ldt9/Stock-Market-BopIt/Enclosure Design Files/ProductImages/IMG_0335.jpg

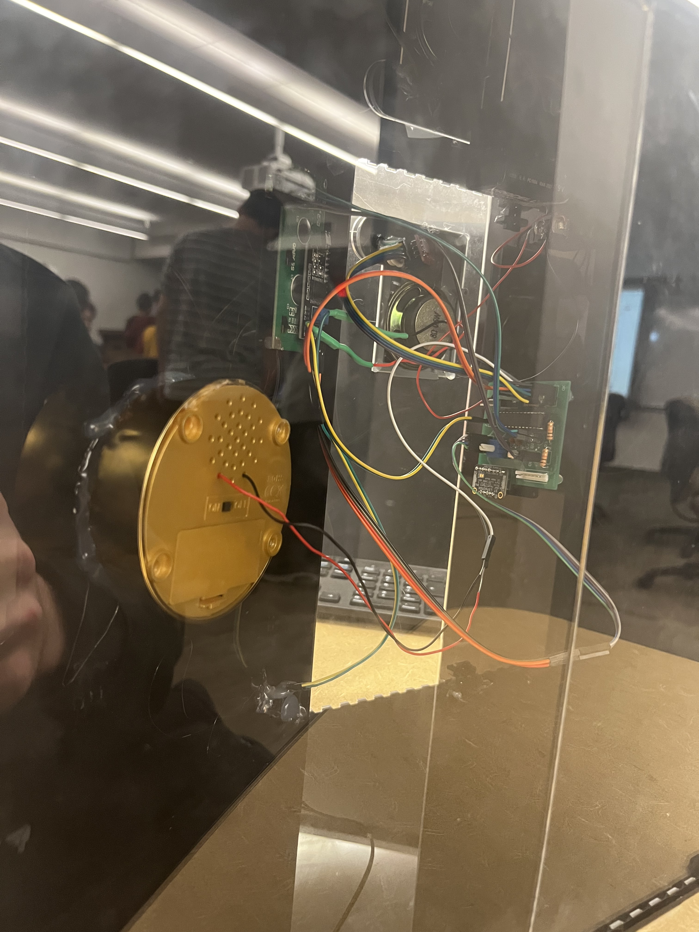
Enclosure Design Files/ProductImages/IMG_0335.jpg
