ldt9/Stock-Market-BopIt/Enclosure Design Files/ProductImages/IMG_0336.jpg

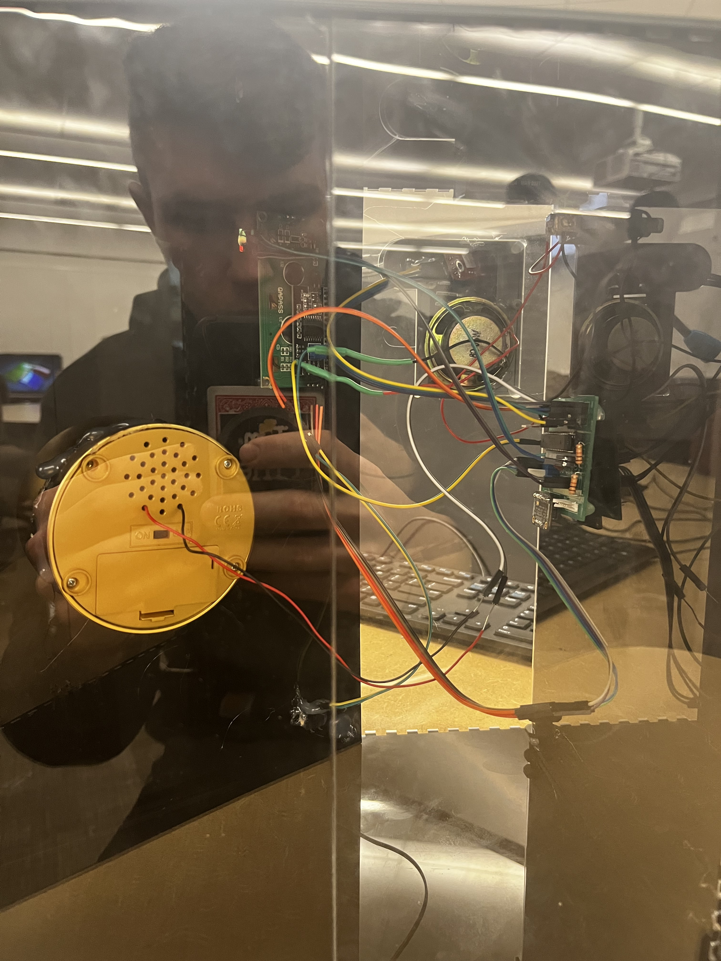
Enclosure Design Files/ProductImages/IMG_0336.jpg
