ldt9/Stock-Market-BopIt/Unit Tests/SimpleAccelerometer.ino

/*
  Arduino LSM6DSOX - Simple Accelerometer

  This example reads the acceleration values from the LSM6DSOX
  sensor and continuously prints them to the Serial Monitor
  or Serial Plotter.

  The circuit:
  - Arduino Nano RP2040 Connect

  created 10 May 2021
  by Arturo Guadalupi

  This example code is in the public domain.
*/

#include <Arduino_LSM6DSOX.h>
#include <LCD_I2C.h>
LCD_I2C lcd(0x27, 16, 2);

void setup() {
  lcd.begin();
  lcd.backlight();
  Serial.begin(9600);
  while (!Serial);

  if (!IMU.begin()) {
    Serial.println("Failed to initialize IMU!");

    while (1);
  }

  Serial.print("Accelerometer sample rate = ");
  Serial.print(IMU.accelerationSampleRate());
  Serial.println(" Hz");
  Serial.println();
  Serial.println("Acceleration in g's");
  Serial.println("X\tY\tZ");
}

void loop() {
  float x, y, z;

  if (IMU.accelerationAvailable()) {
    IMU.readAcceleration(x, y, z);

    lcd.print(x);
    lcd.print('\t');
    lcd.print(y);
    lcd.print('\t');
    lcd.println(z);
  }
}
